frank20a/darkroom-timer/firmware/Darkroom Timer/src/ssd.cpp

#include "ssd.hpp"

bool SSD::begin() {
    // Set proper pin modes and initial states
    pinMode(cs_pin, OUTPUT);
    digitalWrite(cs_pin, HIGH);  // Deselect the display

    // Set SPI settings
    spiSettings = SPISettings(5000000, MSBFIRST, SPI_MODE0); // 5 MHz, MSB first, Mode 0

    // Initialize the display (send any required initialization commands here)
    writeByte(0x09, 0xFF); // Decode mode: all digits
    writeByte(0x0A, 0x04); // Intensity: max brightness 0x00 - 0x0F
    writeByte(0x0B, 0x04); // Scan limit: display 4 digits
    writeByte(0x0C, 0x01); // Shutdown register: normal operation
    writeByte(0x0F, 0x00); // Display test: off

    clear();

    return true;
}

void SSD::setBrightness(uint8_t brightness) {
    if (brightness > 0x0F) 
        brightness = 0x0F;

    writeByte(0x0A, brightness);
}

void SSD::setDigit(uint8_t digit, uint8_t value, bool decimal) {
    if (digit < 1 || digit > 4) {
        return; // Invalid digit index
    }

    if (decimal) {
        value |= 0x80; // Set the decimal point bit
    }

    writeByte(digit, value);
}

void SSD::clear() {
    for (uint8_t i = 1; i <= 4; i++) {
        writeByte(i, 0xF); // Blank character
    }
}

void SSD::setNumber(int number) {
    if (number > 9999 || number < -999) return; // Number too large for 4 digits

    uint8_t digits[4];
    getDigits(number, digits);

    for (uint8_t i = 0; i < 4; i++) {
        setDigit(i + 1, digits[i]);
    }
}

void SSD::setNumber(float number, bool full_decimal) {
    int intNumber;
    int decimalPoints;

    if (full_decimal) {
        if (number > 9999 || number < -999) return; // Number too large for 4 digits

        if (number >= 1000 || number <= -100) {
            number = round(number); // Round to nearest whole number
            intNumber = (int)number;
            decimalPoints = 0;
        } else if (number >= 100 || number <= -10) {
            number = round(number * 10.0) / 10.0; // Round to nearest tenth
            intNumber = (int)(number * 10);
            decimalPoints = 1;
        } else if (number >= 10 || number <= -1) {
            number = round(number * 100.0) / 100.0; // Round to nearest hundredth
            intNumber = (int)(number * 100);
            decimalPoints = 2;
        } else {
            number = round(number * 1000.0) / 1000.0; // Round to nearest thousandth
            intNumber = (int)(number * 1000);
            decimalPoints = 3;
        }
    } else {
        if (number > 999.9 || number < -99.9) return; // Number too large for 4 digits with 1 decimal point
        number = round(number * 10.0) / 10.0; // Round to nearest whole number
        intNumber = (int)(number * 10);
        decimalPoints = 1;
    }
    
    uint8_t digits[4];
    getDigits(intNumber, digits);

    // Keep a leading zero for fractional values, e.g. show 0.9 instead of .9
    if (decimalPoints > 0 && number > -1.0f && number < 1.0f) {
        const uint8_t decimal_digit_index = 3 - decimalPoints;
        digits[decimal_digit_index] = 0; 
    }

    for (uint8_t i = 0; i < 4; i++) {
        setDigit(i + 1, digits[i], i == 3 - decimalPoints && decimalPoints > 0);
    }
}

void SSD::writeByte(uint8_t reg, uint8_t data) {
    SPI.beginTransaction(spiSettings);
    digitalWrite(cs_pin, LOW);
    SPI.transfer16(((uint16_t)reg << 8) | data);
    digitalWrite(cs_pin, HIGH);
    SPI.endTransaction();
}

void SSD::getDigits(int number, uint8_t* digits) {
    bool neg = number < 0;
    number = abs(number);

    digits[0] = number / 1000;
    digits[1] = (number / 100) % 10;
    digits[2] = (number / 10) % 10;
    digits[3] = number % 10;

    digits[2] = (digits[0] || digits[1] || digits[2]) ? digits[2] : 0xF; // Blank leading zero
    digits[1] = (digits[0] || digits[1]) ? digits[1] : 0xF; // Blank leading zero
    digits[0] = digits[0] ? digits[0] : 0xF; // Blank leading zero

    if (neg) {
        if (number > 99)
            digits[0] = 0xA; // '-' symbol for thousands place if number is > 99
        else if (number > 9)
            digits[1] = 0xA; // '-' symbol for hundreds place if number is <= 99
        else
            digits[2] = 0xA; // '-' symbol for tens place if number
    }
}
