frank20a/darkroom-timer/firmware/Darkroom Timer/include/application.hpp

#pragma once


#include <Arduino.h>
#include <SPI.h>
// #include <SD.h>
#include <LittleFS.h>
#include <cstdint>
#include <stdio.h>
#include <bit>

#include "system.hpp"
#include "pin_defs.hpp"
#include "ssd.hpp"
#include "epd.hpp"
#include "encoder.hpp"
#include "tools.hpp"


#define RENDER_INTERVAL_MS      333                 // Minimum interval between screen renders in milliseconds
#define INPUT_READ_INTERVAL     25                  // Minimum interval between input reads in milliseconds
#define LONG_PRESS_THRESH       500                 // Threshold for long press events in milliseconds
#define DIGITAL_INPUT_MASK      0b1111111000000110  // Valid bits for digital inputs, byte 0
#define MAX_SWITCH_POSITIONS    3                   // Maximum number of positions for the switches (0, 1, 2)
#define EVENT_DEBOUNCE_MS       200                 // Number of consecutive reads required to confirm an event
#define RAMP_FACTOR             8e-3                // Ramp factor for light output changes


void print_binary8(uint8_t value);
void print_binary16(uint16_t value);


class Application {
    public:
        Application();

        bool begin();
        void mainloop_step();

    private:
        // Input handling
        void read_inputs();
        void create_input_events();
        void parse_serial_commands();

        // Output handling
        void write_outputs();
        void handle_output_events();

        // Output helper functions
        void set_light_output_focus();
        void set_light_output_setpoint();
        void set_light_output_off();
        int volt_to_analog_value(double voltage);
        int get_analog_output_voltage(int lamp_index = 0);
        
        // Settings management
        bool load_settings();
        void save_settings();
        void reset_settings();

        SystemState system;
        
        EPD_Display *epd;
        Encoder *encoder;
        SSD *ssd;

        float voltage_setpoints[3] = {0, 0, 0};
        RampLinear _p_ramp[3] = {
            RampLinear(RAMP_FACTOR),
            RampLinear(RAMP_FACTOR),
            RampLinear(RAMP_FACTOR)
        };
};
