frank20a/darkroom-timer/firmware/Darkroom Timer/include/string_const.hpp

#pragma once


#define NUM_SETTINGS_MENU_ITEMS 15
#define LIGHT_SOURCE_OPTIONS 4
#define AO_FUNCTION_OPTIONS 4


namespace string_const {
    static const char* LightSources[] = {
        "None",
        "Lamp",
        "Single Analog",
        "Triple Analog"
    };

    static const char* AOFunctions[] = {
        // "Linear",
        // "Exponential",
        // "Polynomial 2",
        // "Polynomial 3"
        "y=ax+b",
        "y=a2^(bx)",
        "y=ax^2+bx+c",
        "y=ax^3+bx^2+cx+d"
    };

    static const char* SettingsMenuItems[] = {
        "\\/ Save Settings",
        "F-Stop Table",
        "Light Source",
        "7SD Brightness",
        "Buzzer Frequency",
        "AO Function",
        "AO Voltage Limit",
        "AO Voltage Input",
        "AO Coeffs #1",
        "AO Coeffs #2",
        "AO Coeffs #3",
        "AO Coeffs #4",
        "AO Range LOW",
        "AO Range HIGH",
        "About",
        "/\\ Reset Settings !!!"
    };

    static const char* cmyk_labels[3] = {"yellow", "magenta", "cyan"};
    static const char* rgb_labels[3] = {"blue", "green", "red"};
    
    static const char* table_labels[7] = {"0", "1/6", "1/4", "1/3", "1/2", "2/3", "3/4"};


    static const char* preview_states[3] = {"off", "preview", "focus"};
};
