frank20a/darkroom-timer/firmware/Darkroom Timer/include/assets.hpp

#pragma once
#include <stdint.h>

struct epd_image_t{
    unsigned char *data;
    uint16_t width;
    uint16_t height;
};

namespace Assets {
    extern const epd_image_t penis;
    extern const epd_image_t calculator;
    extern const epd_image_t floppy;
    extern const epd_image_t light;
    extern const epd_image_t gear;
    extern const epd_image_t clock;
    extern const epd_image_t big_lamp_on;
    extern const epd_image_t big_lamp_off;
    extern const epd_image_t big_check;
    extern const epd_image_t big_time;
    extern const epd_image_t big_recycle;
    extern const epd_image_t big_bars;
    extern const epd_image_t big_playpause;
};
